Shamekh21/Line-Follower-Robot-PID-Control/CAD/motor.STEP

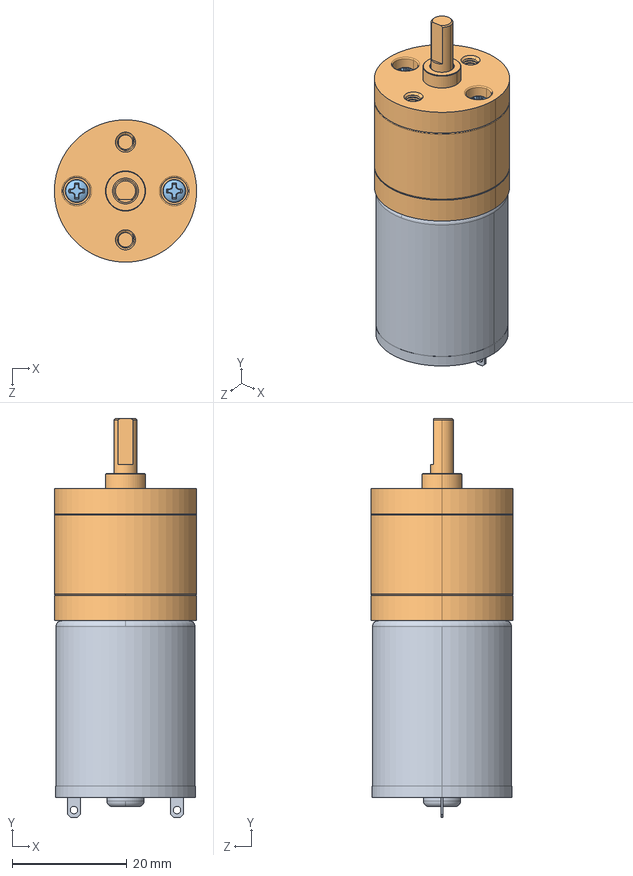
[picture p10: CAD file, 2026-06-14]
CAD/motor.STEP
24.8 x 69.5 x 24.8 mm
Motor.step
Gearbox.step
90116A027_316 Stainless Steel Pan Head Phillips Screws.step x 2
